bitaxeorg/bitaxeproto/3d/DISST7789-176x320.STEP

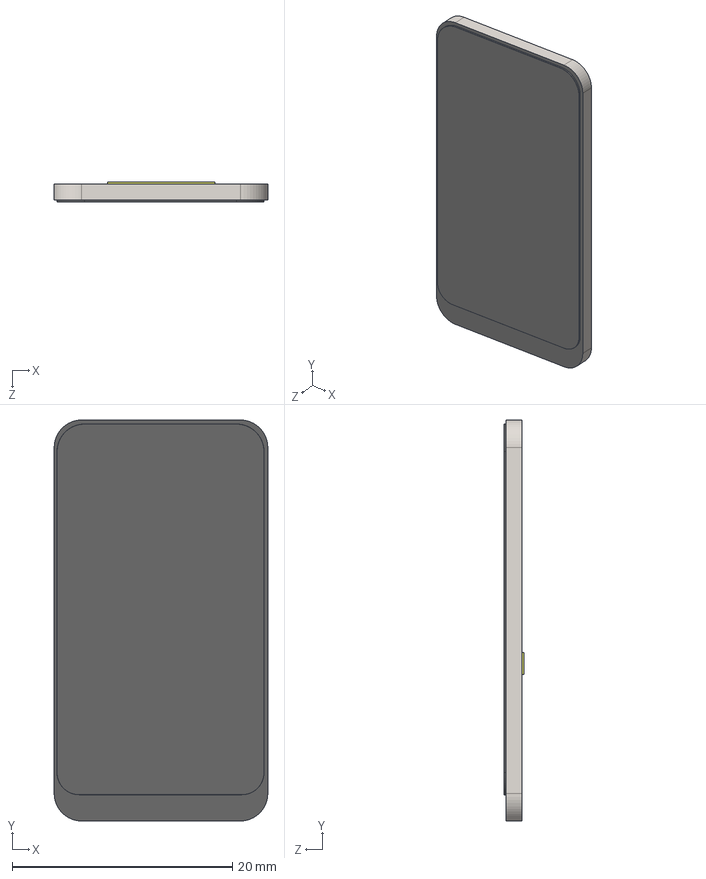
[picture p16: CAD file, 2026-05-12]
3d/DISST7789-176x320.STEP
19.4 x 36.4 x 1.86 mm
