bitaxeorg/bitaxeproto/3d/TXB0104RGYR.STEP

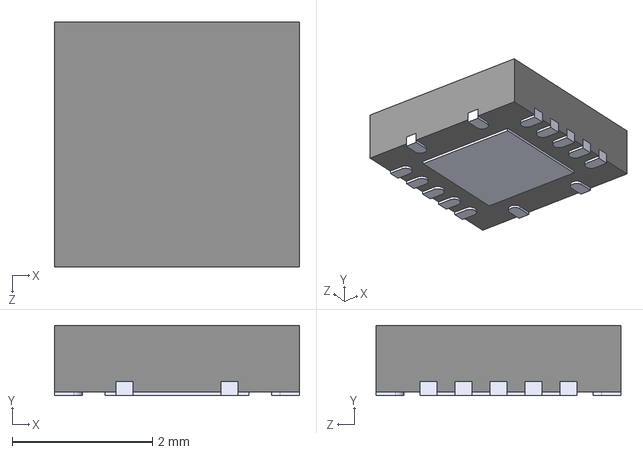
[picture p17: CAD file, 2026-05-12]
3d/TXB0104RGYR.STEP
3.50 x 1.00 x 3.50 mm
