bitaxeorg/bitaxeproto/3d/ESP32-S3-WROOM-1-N8R2--3DModel-STEP-56544.STEP

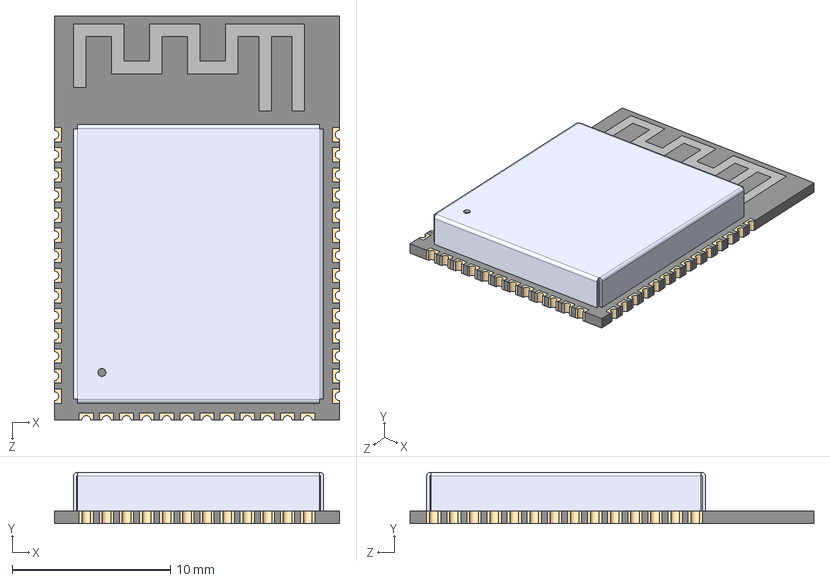
[picture p18: CAD file, 2026-05-12]
3d/ESP32-S3-WROOM-1-N8R2--3DModel-STEP-56544.STEP
18.0 x 3.25 x 25.5 mm
