bitaxeorg/bitaxeproto/3d/TPS546D24ARVFR.step

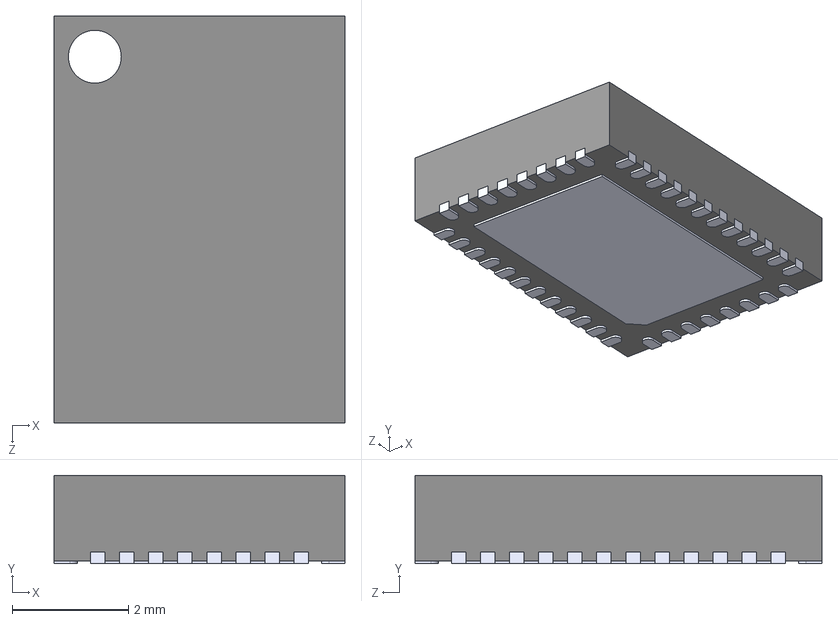
[picture p19: CAD file, 2026-05-12]
3d/TPS546D24ARVFR.step
5.00 x 1.52 x 7.00 mm
