bitaxeorg/bitaxeproto/3d/BitaxeGT_heatsink.step

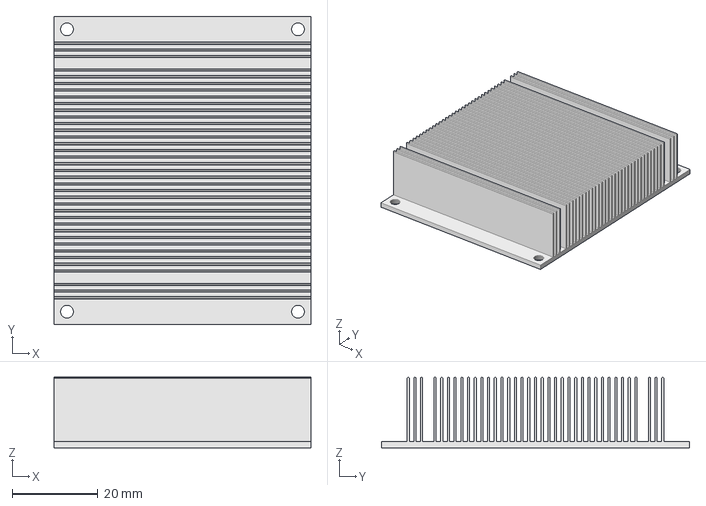
[picture p20: CAD file, 2026-05-12]
3d/BitaxeGT_heatsink.step
60.0 x 72.0 x 16.5 mm
