bitaxeorg/bitaxeproto/3d/BM04B-SRSS-TB.STEP

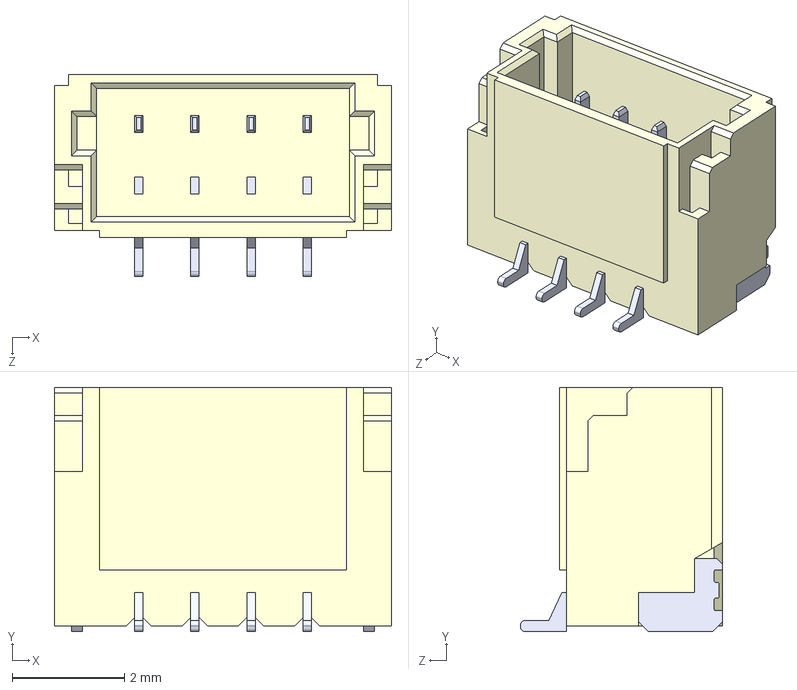
[picture p21: CAD file, 2026-05-12]
3d/BM04B-SRSS-TB.STEP
6.00 x 4.35 x 3.60 mm
