bitaxeorg/bitaxeproto/3d/ECS-3225MV-500-CN-TR.STEP

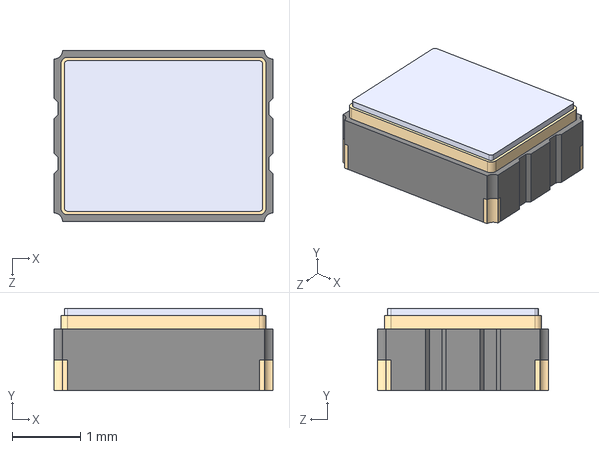
[picture p22: CAD file, 2026-05-12]
3d/ECS-3225MV-500-CN-TR.STEP
3.20 x 1.20 x 2.50 mm
