bitaxeorg/bitaxeproto/3d/BM1368xx.stp

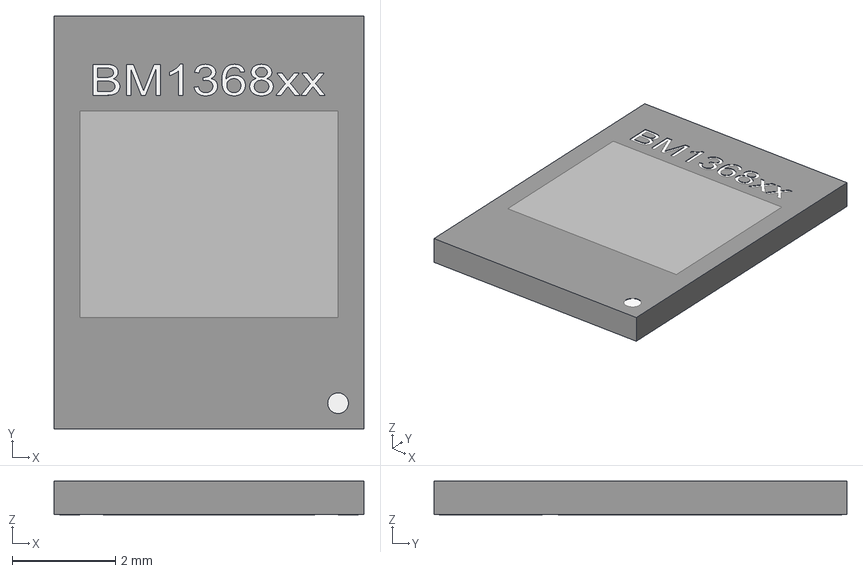
[picture p23: CAD file, 2026-05-12]
3d/BM1368xx.stp
6.00 x 8.00 x 0.65 mm
