bitaxeorg/bitaxeproto/3d/CUI_DEVICES_PJ-036AH-SMT-TR.step

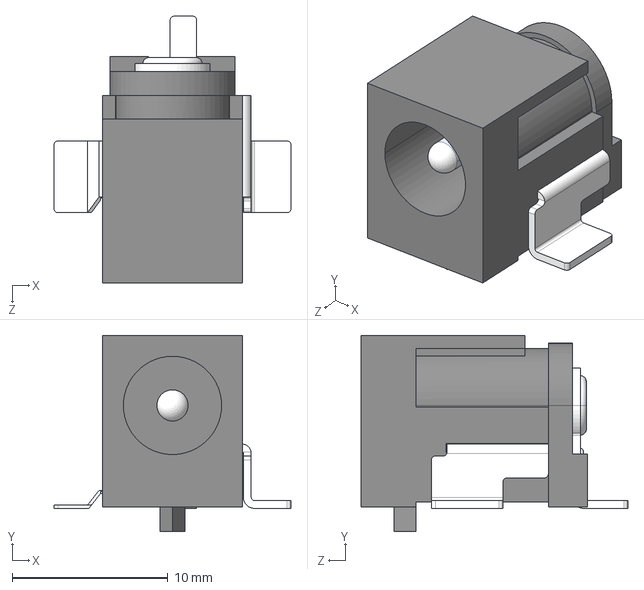
[picture p24: CAD file, 2026-05-12]
3d/CUI_DEVICES_PJ-036AH-SMT-TR.step
15.2 x 12.6 x 17.1 mm
