bitaxeorg/bitaxeproto/3d/SLC1175-271MEC_COC.step

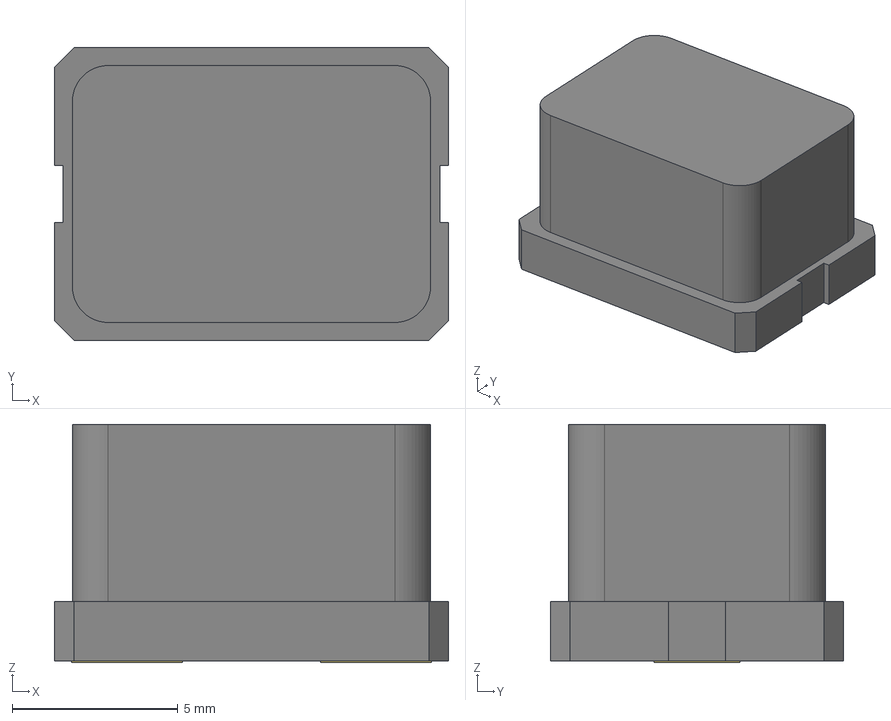
[picture p25: CAD file, 2026-05-12]
3d/SLC1175-271MEC_COC.step
11.9 x 8.83 x 7.19 mm
