bitaxeorg/bitaxeproto/3d/FPC-SMD_P0.50-8P_FGS-XJ-H2.0.step

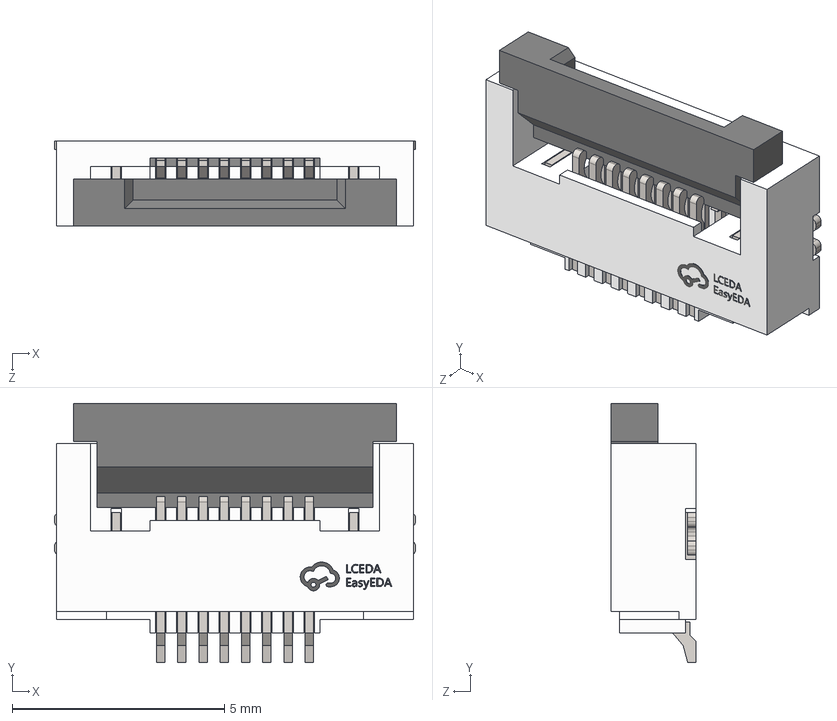
[picture p26: CAD file, 2026-05-12]
3d/FPC-SMD_P0.50-8P_FGS-XJ-H2.0.step
8.50 x 6.10 x 2.01 mm
