bitaxeorg/bitaxeproto/3d/USB_10118193-0001LF.STEP

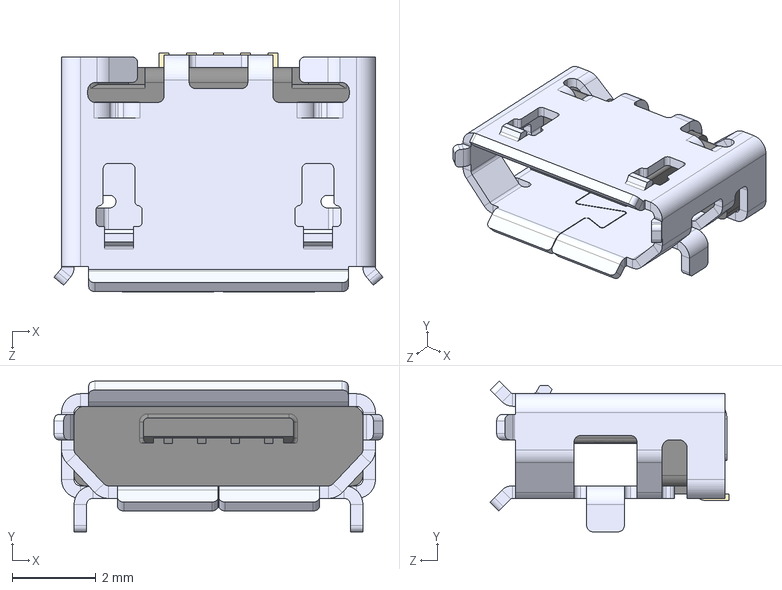
[picture p27: CAD file, 2026-05-12]
3d/USB_10118193-0001LF.STEP
7.86 x 3.60 x 5.71 mm
