bitaxeorg/bitaxeproto/3d/TPSM863257RDXR--3DModel-STEP-510211.STEP

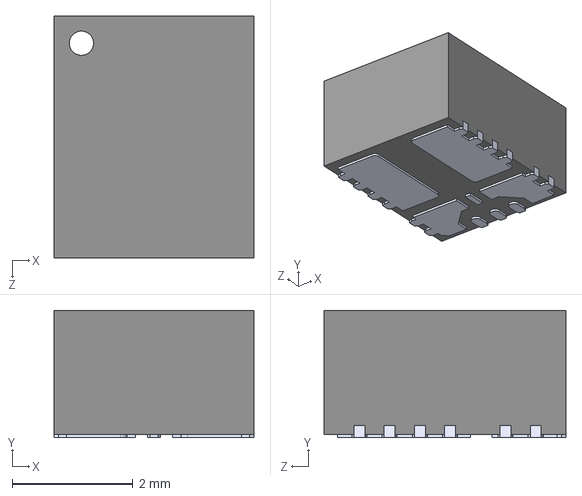
[picture p29: CAD file, 2026-05-12]
3d/TPSM863257RDXR--3DModel-STEP-510211.STEP
3.30 x 2.10 x 4.00 mm
