bitaxeorg/bitaxeproto/3d/TSOT-23-5_RIT.step

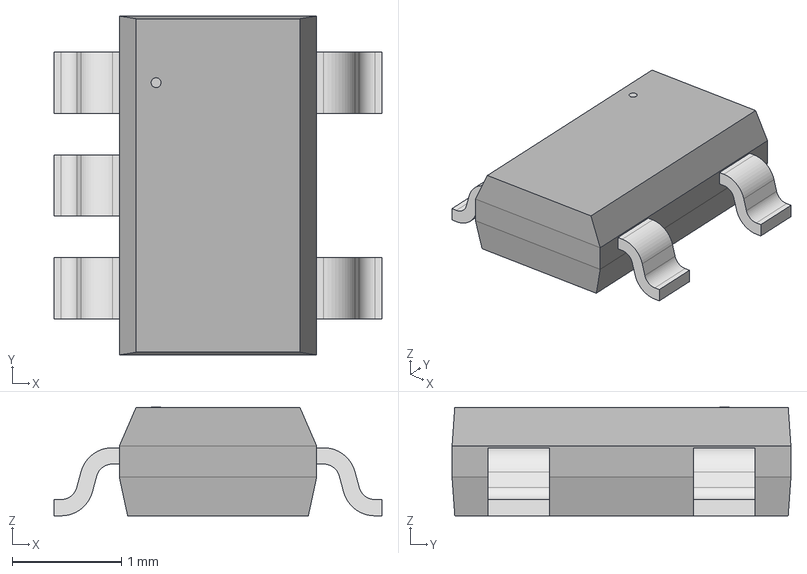
[picture p30: CAD file, 2026-05-12]
3d/TSOT-23-5_RIT.step
3.00 x 3.10 x 0.993 mm
