bitaxeorg/bitaxeproto/3d/RGY0016A.stp

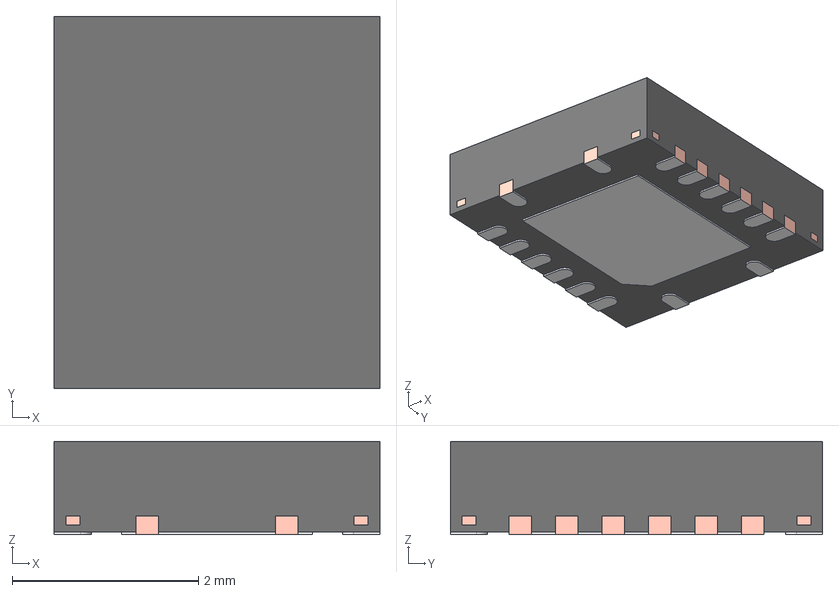
[picture p31: CAD file, 2026-05-12]
3d/RGY0016A.stp
3.50 x 4.00 x 1.00 mm
FRAME
PIN1_AREA
