bitaxeorg/bitaxeproto/3d/FFC2B35-08-T.STEP

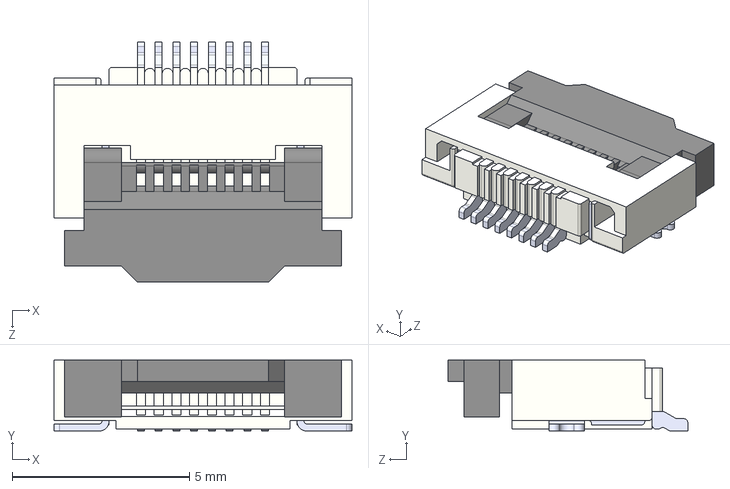
[picture p32: CAD file, 2026-05-12]
3d/FFC2B35-08-T.STEP
8.40 x 2.00 x 6.76 mm
