bitaxeorg/bitaxeproto/3d/XTAL_SC32S-7PF20PPM_EPS.step

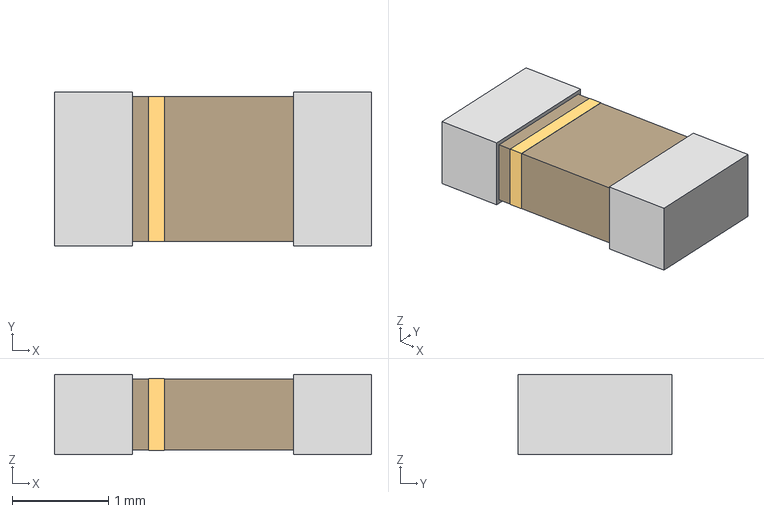
[picture p34: CAD file, 2026-05-12]
3d/XTAL_SC32S-7PF20PPM_EPS.step
3.30 x 1.60 x 0.838 mm
