bitaxeorg/bitaxeproto/3d/BQB0016A.stp

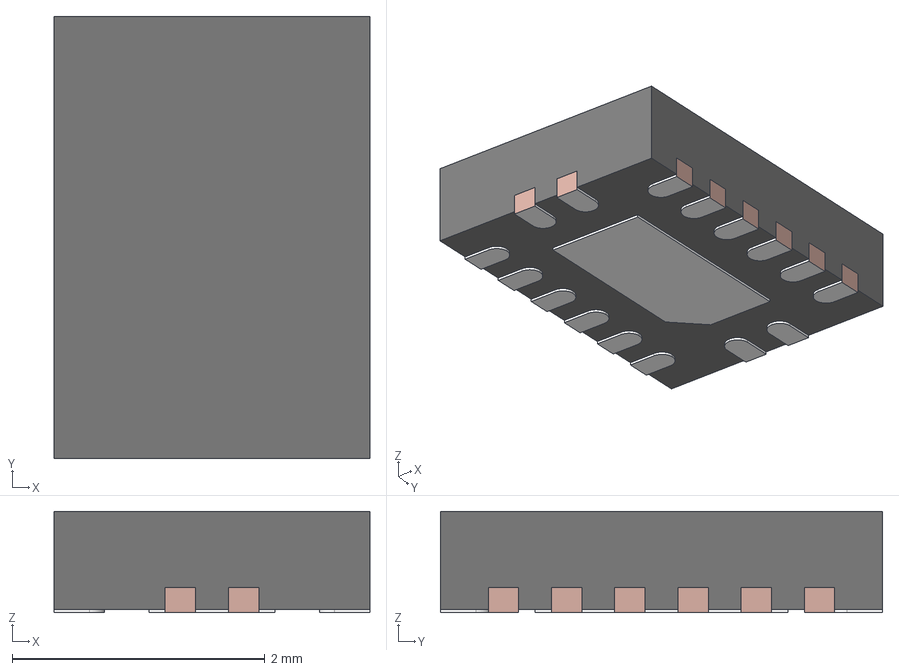
[picture p35: CAD file, 2026-05-12]
3d/BQB0016A.stp
2.50 x 3.50 x 0.8 mm
FRAME
