bitaxeorg/bitaxeproto/3d/RP-006426-DD-A-Raspberry Pi Pico 2 3D CAD Model R5 24 07 24.step

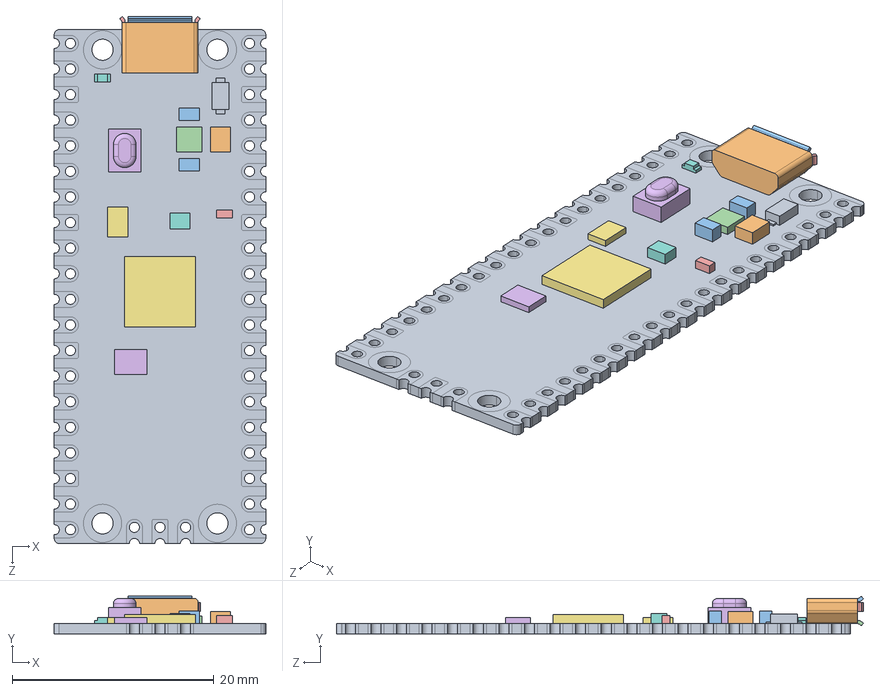
[picture p37: CAD file, 2026-05-12]
3d/RP-006426-DD-A-Raspberry Pi Pico 2 3D CAD Model R5 24 07 24.step
21.0 x 3.73 x 52.3 mm
PICO_REF_BOARD
PICO_REF_USB
PICO_REF_SWITCH
PICO_REF_MICROCONTROLLER
PICO_REF_LED
PICO_REF_COMP_1
PICO_REF_COMP_2
PICO_REF_COMP_3 x 2
PICO_REF_COMP_4
PICO_REF_COMP_5
PICO_REF_COMP_6
PICO_REF_COMP_7
PICO_REF_INDUCTOR
