bitaxeorg/bitaxeproto/3d/SOT-23-5_M5_MCH.step

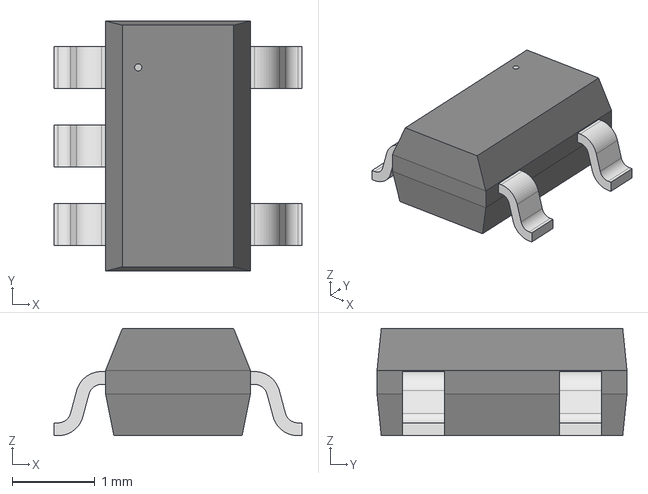
[picture p38: CAD file, 2026-05-12]
3d/SOT-23-5_M5_MCH.step
3.00 x 3.02 x 1.30 mm
