bitaxeorg/bitaxeproto/3d/RaspberryPi_Pico_W_AddedHeaders.step

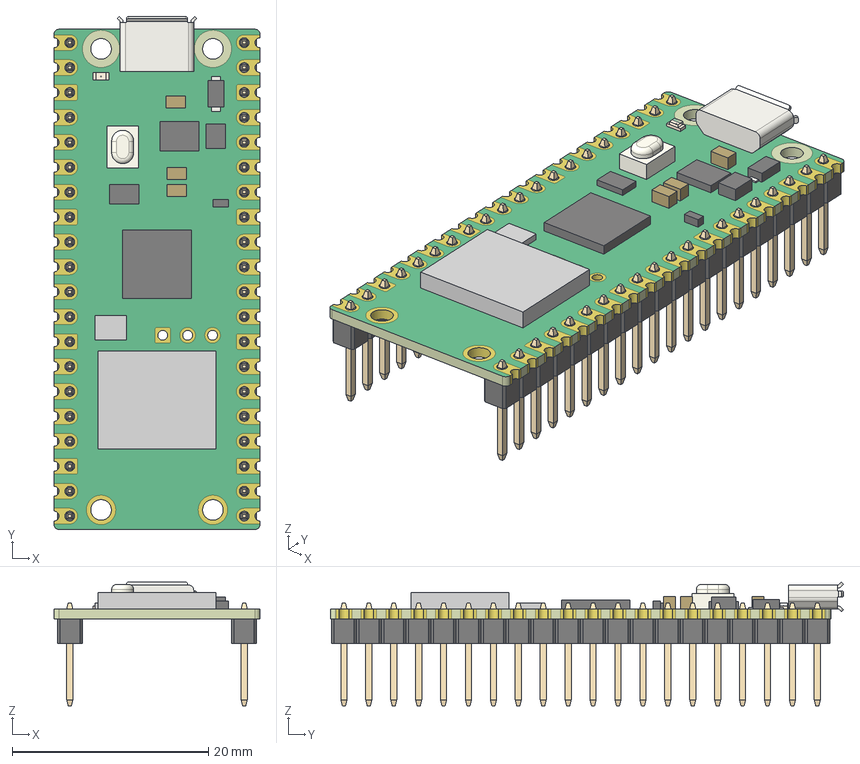
[picture p39: CAD file, 2026-05-12]
3d/RaspberryPi_Pico_W_AddedHeaders.step
21.0 x 52.3 x 12.6 mm
