bitaxeorg/bitaxeproto/3d/GT heatsink.step

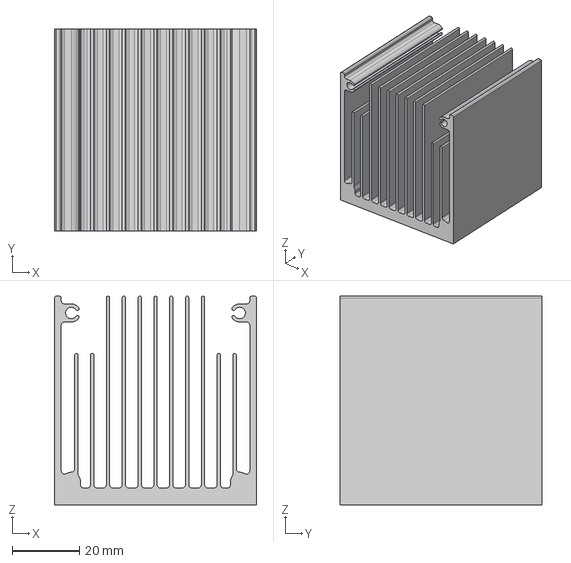
[picture p40: CAD file, 2026-05-12]
3d/GT heatsink.step
60.0 x 60.0 x 62.0 mm
