bitaxeorg/bitaxeproto/3d/DQH0008A.stp

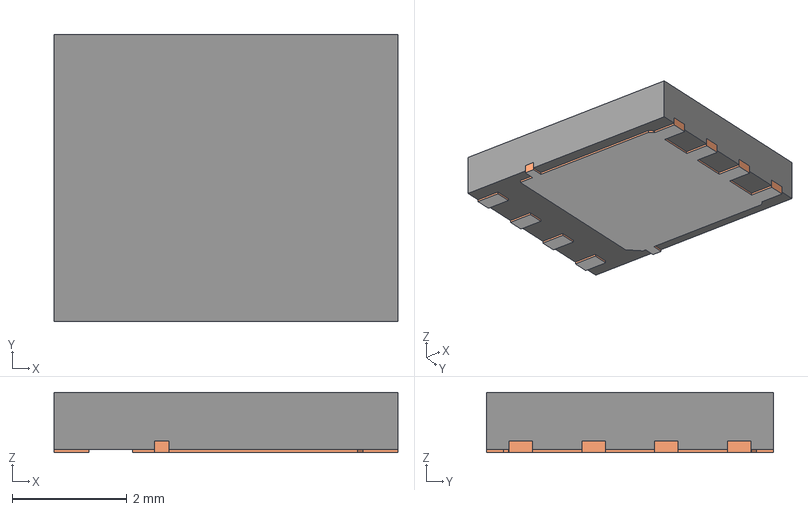
[picture p41: CAD file, 2026-05-12]
3d/DQH0008A.stp
6.00 x 5.00 x 1.05 mm
BODY-SON
FRAME-DQH0008A
PIN1-ID
