bitaxeorg/bitaxeproto/3d/DHVQFN14_SOT762-1_NEX.step

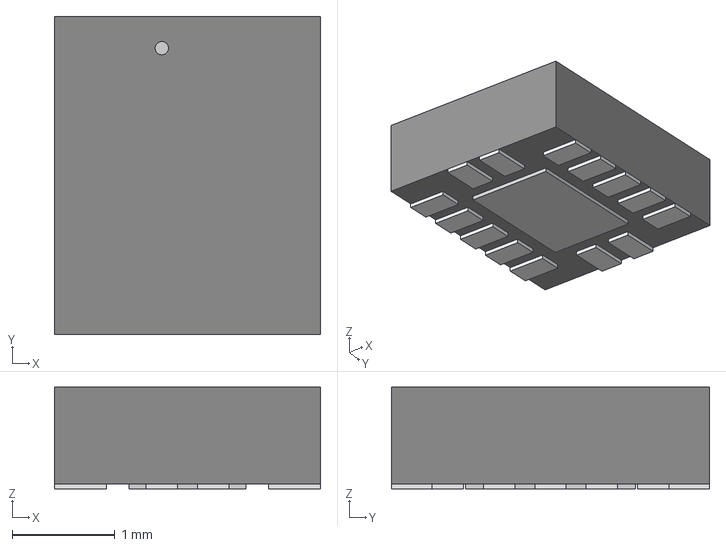
[picture p42: CAD file, 2026-05-12]
3d/DHVQFN14_SOT762-1_NEX.step
2.59 x 3.10 x 0.993 mm
