bitaxeorg/bitaxeproto/3d/Bitaxe_Heatsink.step

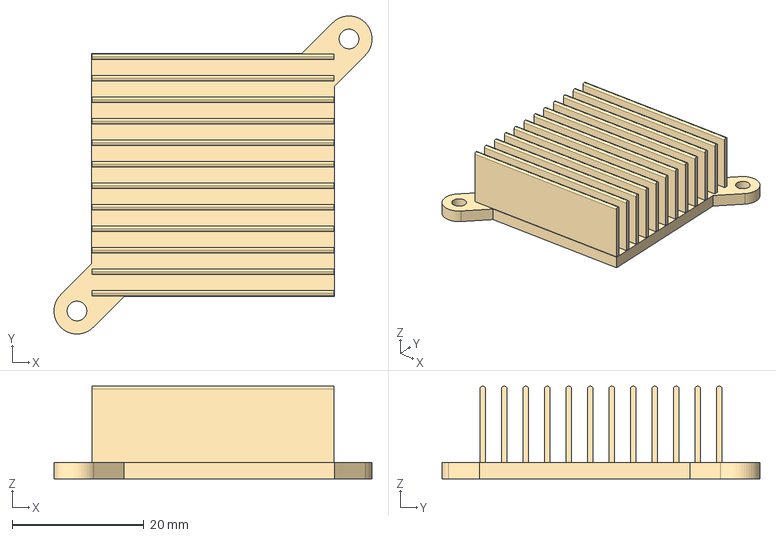
[picture p43: CAD file, 2026-05-12]
3d/Bitaxe_Heatsink.step
48.4 x 48.4 x 14.1 mm
