bitaxeorg/bitaxeproto/3d/oscillator3.2x2.5.step

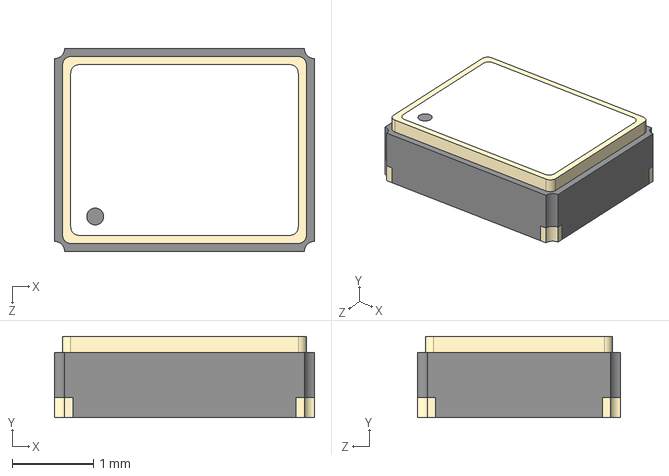
[picture p44: CAD file, 2026-05-12]
3d/oscillator3.2x2.5.step
3.20 x 1.00 x 2.50 mm
