bitaxeorg/bitaxeproto/3d/TPSM82903SISR.stp

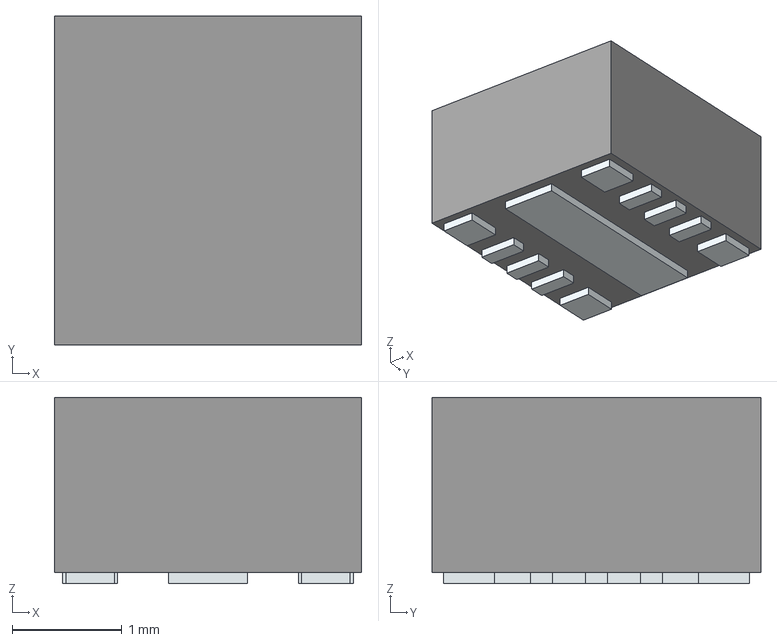
[picture p45: CAD file, 2026-05-12]
3d/TPSM82903SISR.stp
2.80 x 3.00 x 1.70 mm
Pins
