bitaxeorg/bitaxeproto/3d/c-63862-1-r-3d.stp

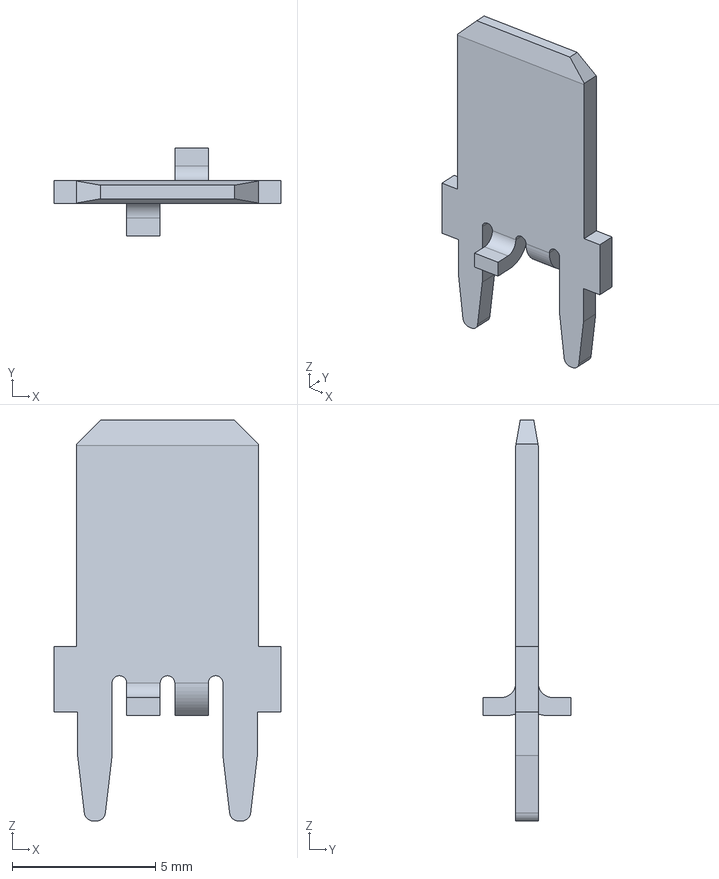
[picture p46: CAD file, 2026-05-12]
3d/c-63862-1-r-3d.stp
7.92 x 3.07 x 14.0 mm
