bitaxeorg/bitaxeproto/3d/2R5TPE220MAFB.step

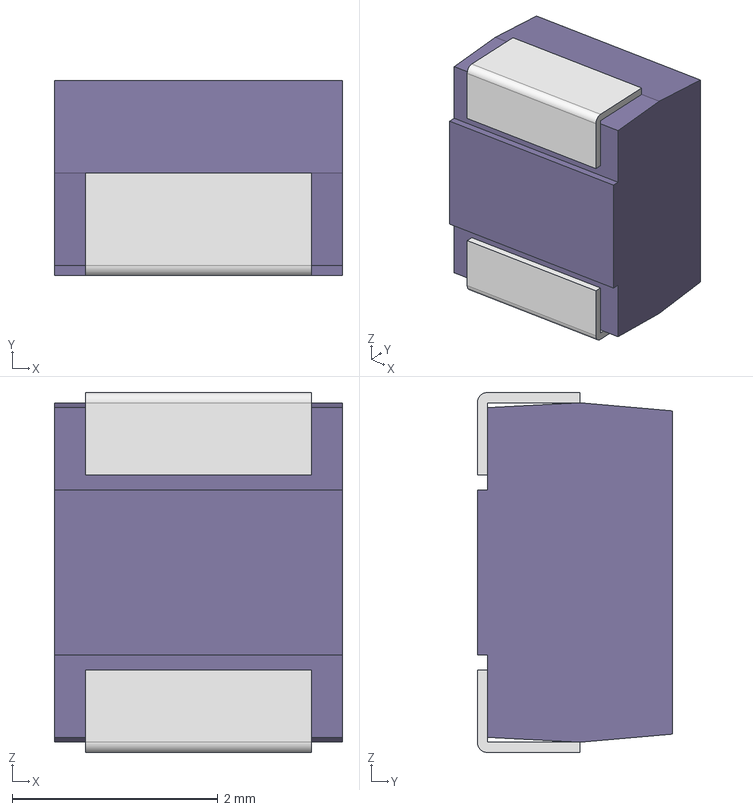
[picture p47: CAD file, 2026-05-12]
3d/2R5TPE220MAFB.step
2.80 x 1.90 x 3.50 mm
mold-B2
flame-B2 x 2
