bitaxeorg/bitaxeproto/3d/USON-8_UX_2x3x0p6_WIN.step

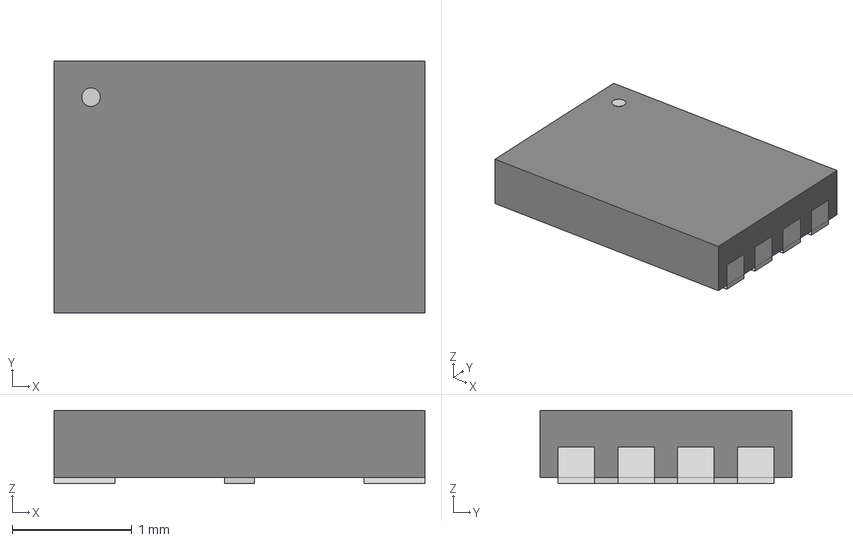
[picture p48: CAD file, 2026-05-12]
3d/USON-8_UX_2x3x0p6_WIN.step
3.10 x 2.11 x 0.612 mm
