bitaxeorg/bitaxeproto/3d/CS1213AG-tr.stp

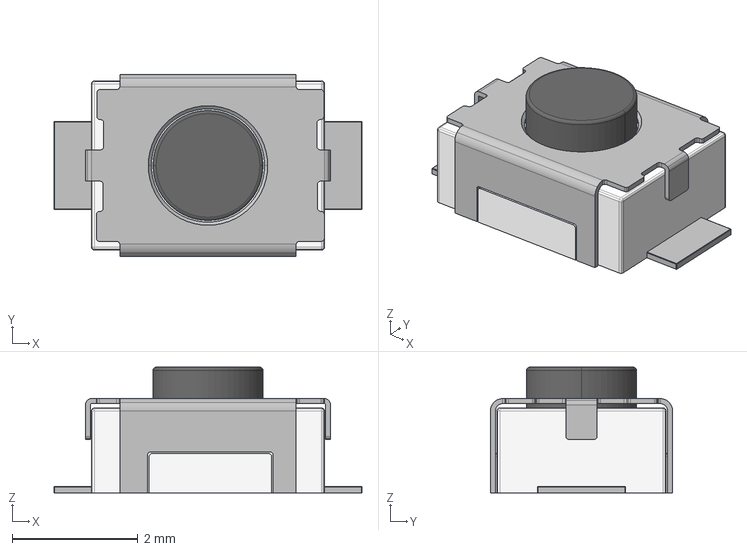
[picture p49: CAD file, 2026-05-12]
3d/CS1213AG-tr.stp
4.90 x 2.90 x 2.00 mm
