bitaxeorg/bitaxeproto/3d/Crystal_3225.step

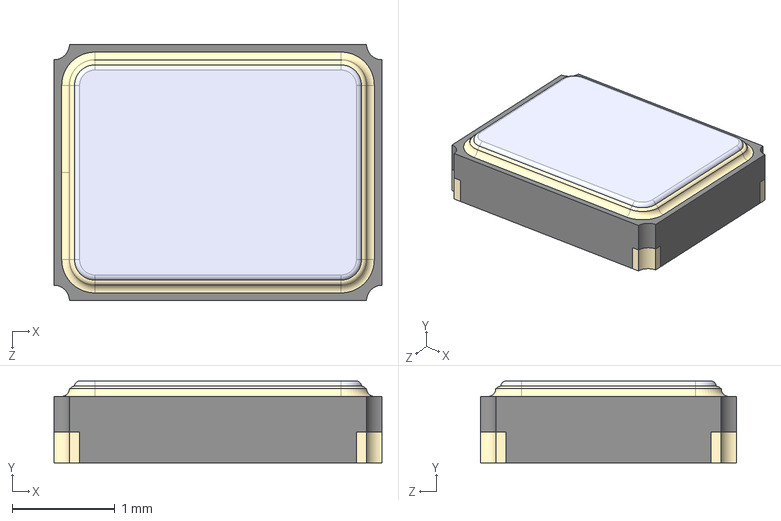
[picture p51: CAD file, 2026-05-12]
3d/Crystal_3225.step
3.20 x 0.8 x 2.50 mm
