bitaxeorg/bitaxeproto/3d/SN74AXC1T45DBVR.STEP

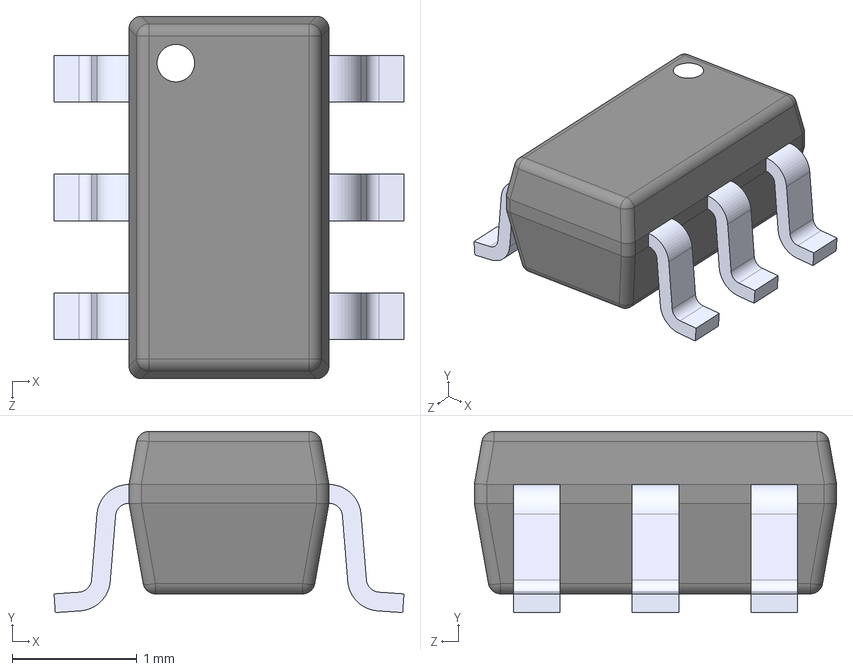
[picture p53: CAD file, 2026-05-12]
3d/SN74AXC1T45DBVR.STEP
2.80 x 1.45 x 2.90 mm
