bitaxeorg/bitaxeproto/3d/141_TL3330AFxxxQG.stp

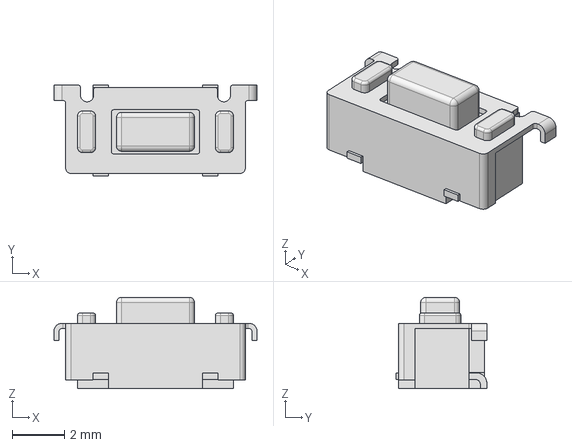
[picture p55: CAD file, 2026-05-12]
3d/141_TL3330AFxxxQG.stp
7.80 x 3.50 x 3.51 mm
