bitaxeorg/bitaxeproto/3d/c-1-1735042-0-m-3d.stp

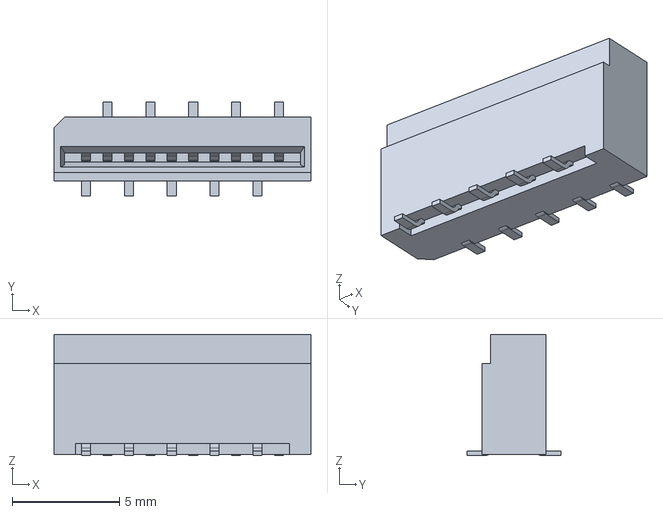
[picture p57: CAD file, 2026-05-12]
3d/c-1-1735042-0-m-3d.stp
12.0 x 4.40 x 5.65 mm
