bitaxeorg/bitaxeproto/3d/21-0164B_L622-1_MXM.step

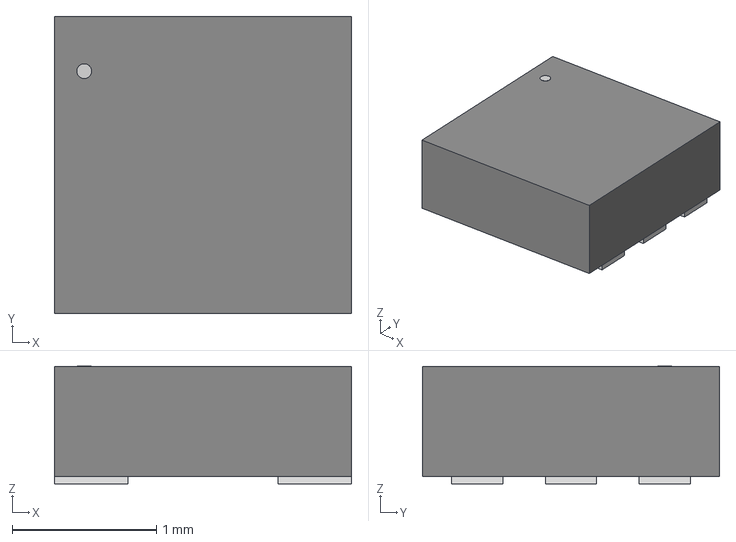
[picture p58: CAD file, 2026-05-12]
3d/21-0164B_L622-1_MXM.step
2.06 x 2.06 x 0.815 mm
