bitaxeorg/bitaxeproto/3d/SOD-323FL_UMD2__ROM.step

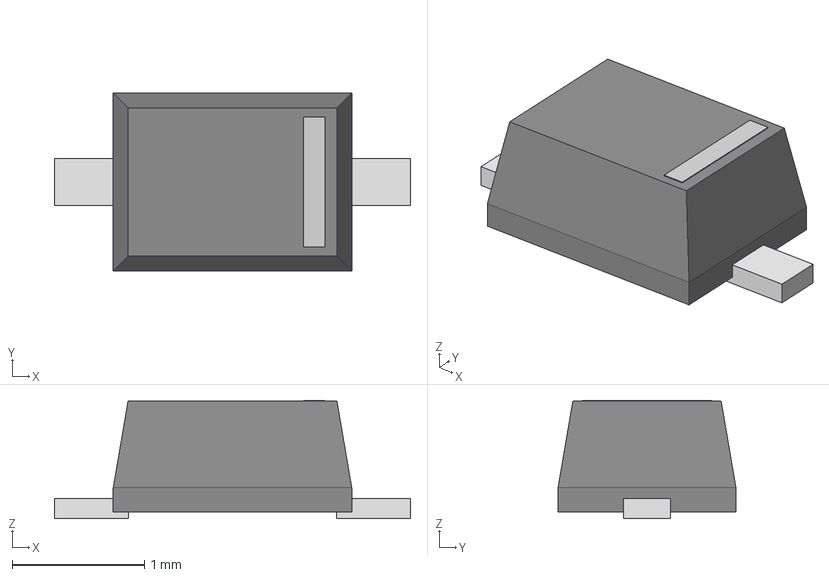
[picture p60: CAD file, 2026-05-12]
3d/SOD-323FL_UMD2__ROM.step
2.69 x 1.35 x 0.895 mm
