bitaxeorg/bitaxeproto/3d/CUI_DEVICES_PJ-002AH.step

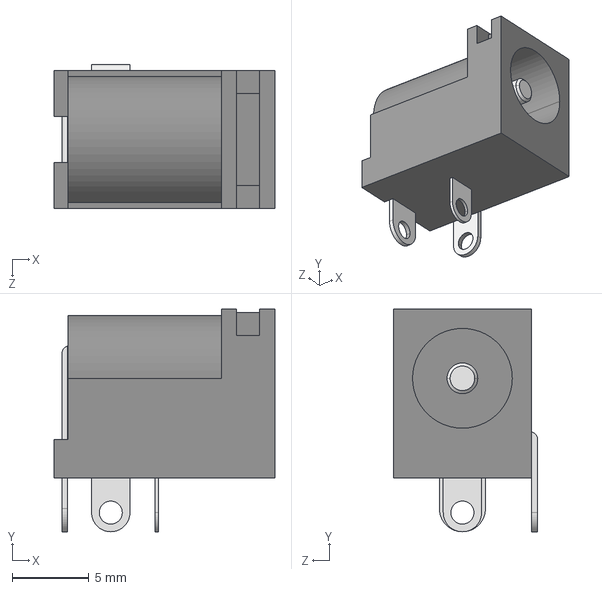
[picture p61: CAD file, 2026-05-12]
3d/CUI_DEVICES_PJ-002AH.step
14.4 x 14.5 x 9.40 mm
