bitaxeorg/bitaxeproto/3d/CUI_DEVICES_PJ-037AH.step

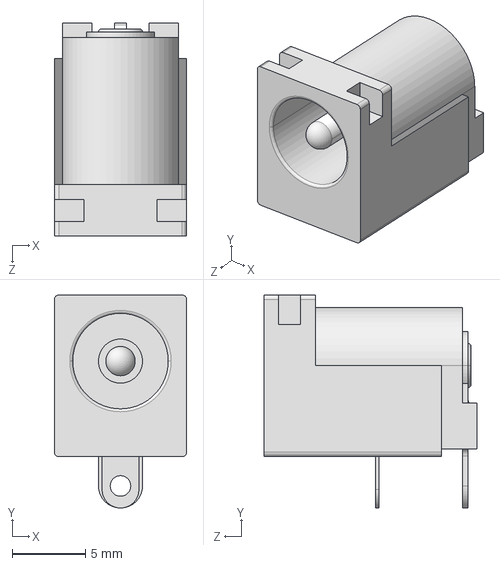
[picture p62: CAD file, 2026-05-12]
3d/CUI_DEVICES_PJ-037AH.step
9.00 x 14.5 x 14.5 mm
