bitaxeorg/bitaxeproto/3d/SMV_z90.stp

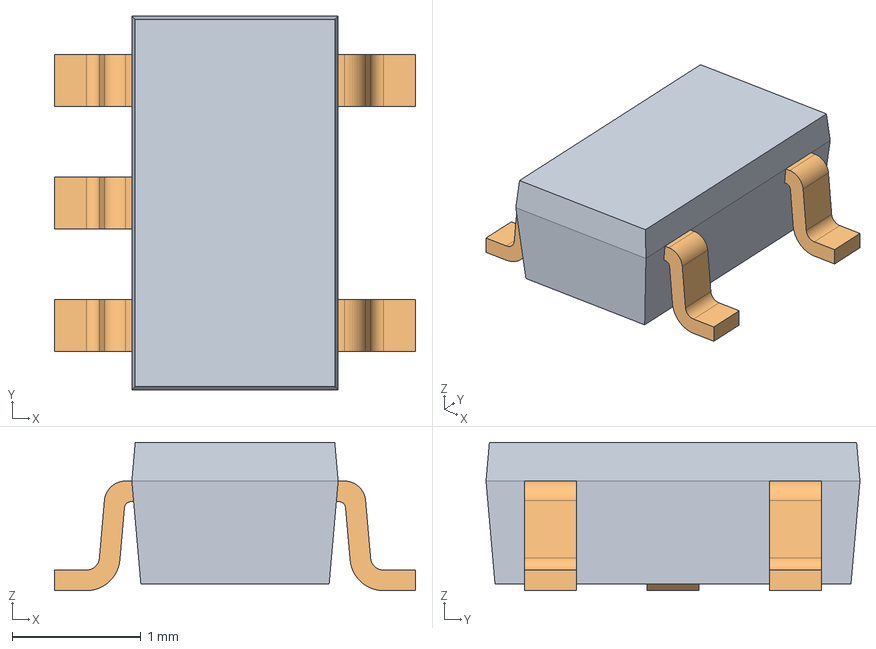
[picture p64: CAD file, 2026-05-12]
3d/SMV_z90.stp
2.80 x 2.90 x 1.15 mm
