bitaxeorg/bitaxeproto/3d/XRCGB27M120F3M10R0_MUR.step

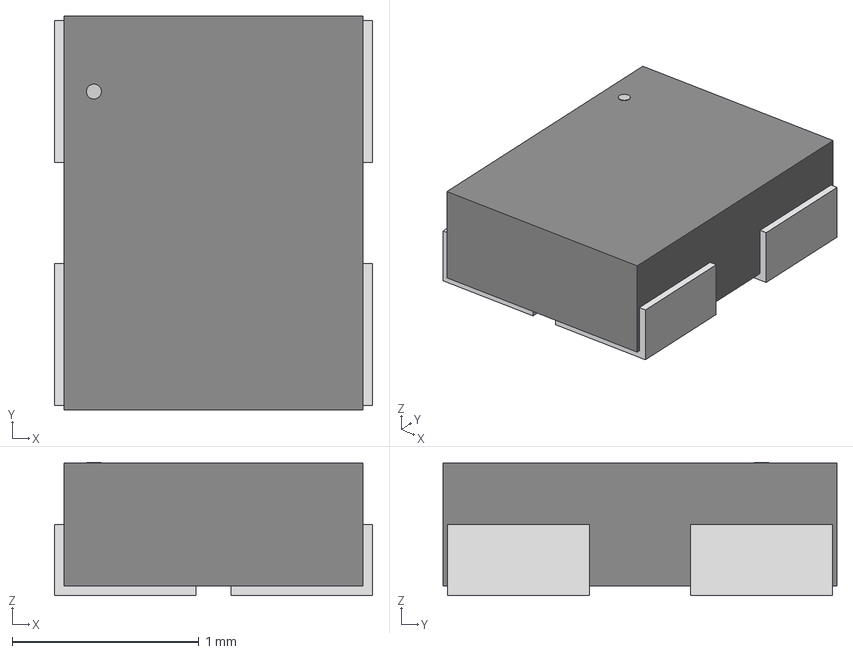
[picture p65: CAD file, 2026-05-12]
3d/XRCGB27M120F3M10R0_MUR.step
1.70 x 2.11 x 0.714 mm
