bitaxeorg/bitaxeproto/3d/DQN0004A.stp

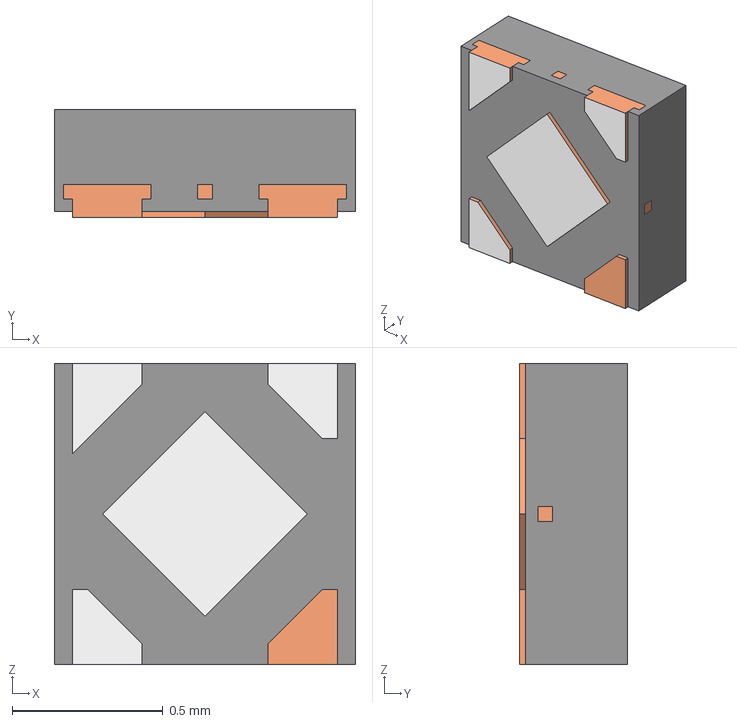
[picture p68: CAD file, 2026-05-12]
3d/DQN0004A.stp
1.00 x 0.36 x 1.00 mm
MOLD-SNB04A
FRAME-SNB04A
