bitaxeorg/bitaxeproto/3d/IND_-1R5MC_SUM.step

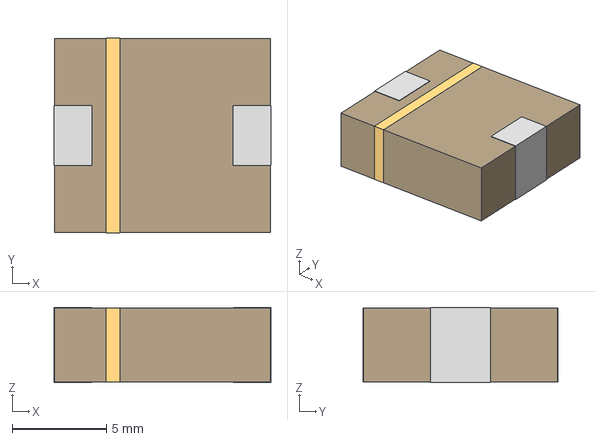
[picture p69: CAD file, 2026-05-12]
3d/IND_-1R5MC_SUM.step
11.5 x 10.3 x 3.99 mm
