bitaxeorg/bitaxeproto/3d/XT30PW-M.stp

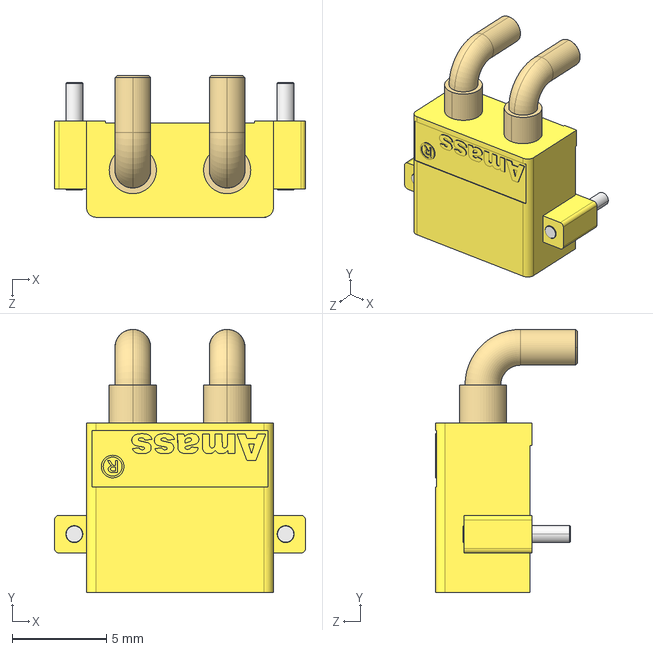
[picture p70: CAD file, 2026-05-12]
3d/XT30PW-M.stp
13.3 x 13.9 x 7.50 mm
