bitaxeorg/bitaxeproto/3d/Coilcraft-XAL1060.STEP

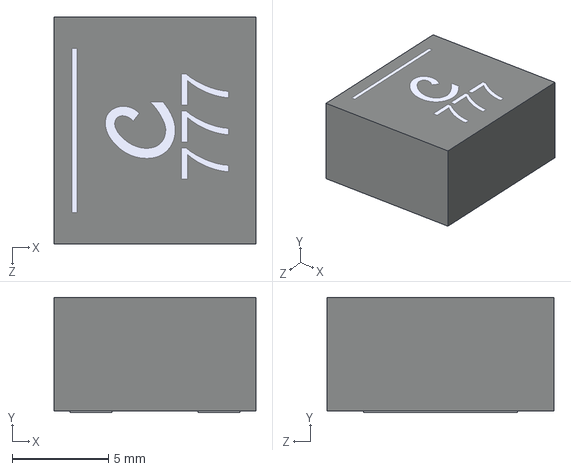
[picture p71: CAD file, 2026-05-12]
3d/Coilcraft-XAL1060.STEP
10.5 x 6.00 x 11.8 mm
