bitaxeorg/bitaxeproto/3d/bm1370.step

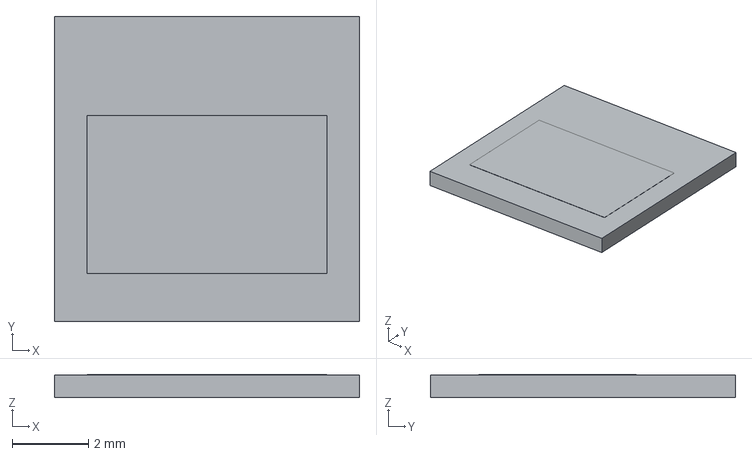
[picture p73: CAD file, 2026-05-12]
3d/bm1370.step
8.00 x 8.00 x 0.61 mm
