bitaxeorg/bitaxeproto/3d/DRL0006A.stp

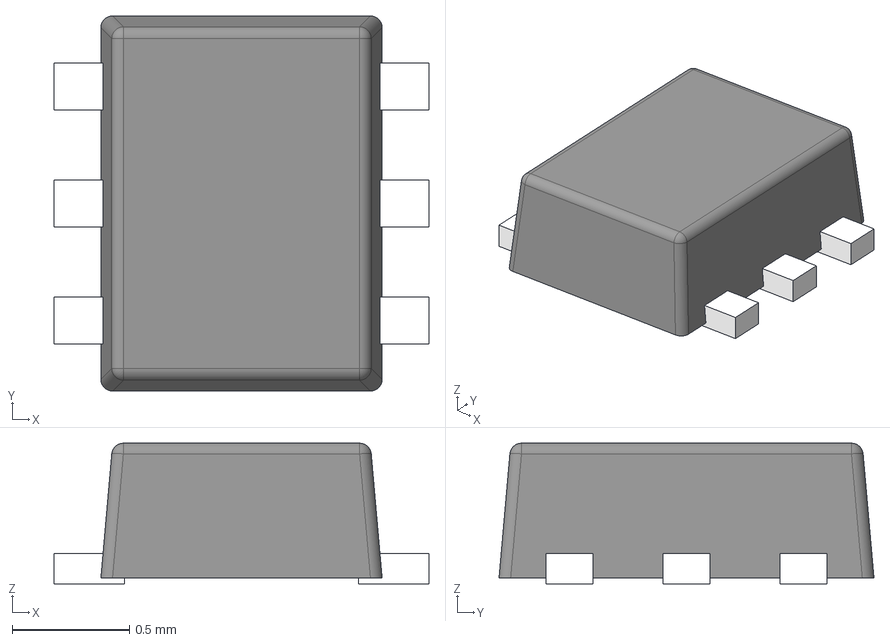
[picture p74: CAD file, 2026-05-12]
3d/DRL0006A.stp
1.60 x 1.60 x 0.6 mm
FRAME-DRL0006A
BODY-SOT
PIN1-ID
