bitaxeorg/bitaxeproto/3d/QFN16_4X4_MCH.step

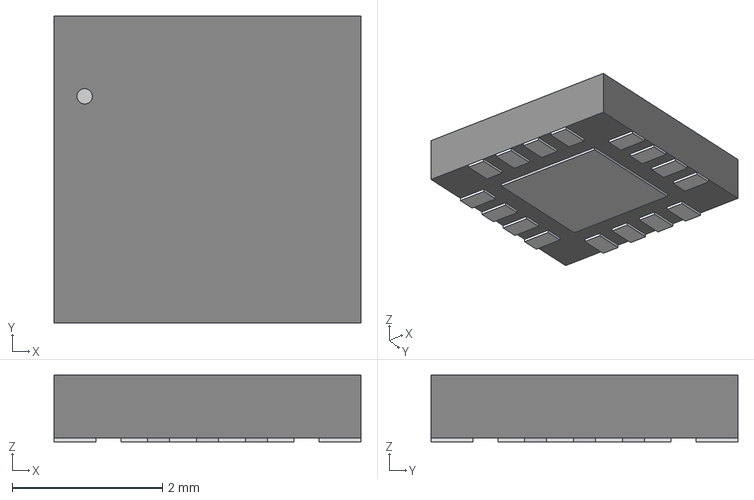
[picture p75: CAD file, 2026-05-12]
3d/QFN16_4X4_MCH.step
4.09 x 4.09 x 0.892 mm
