bitaxeorg/bitaxeproto/3d/DCK0006A.stp

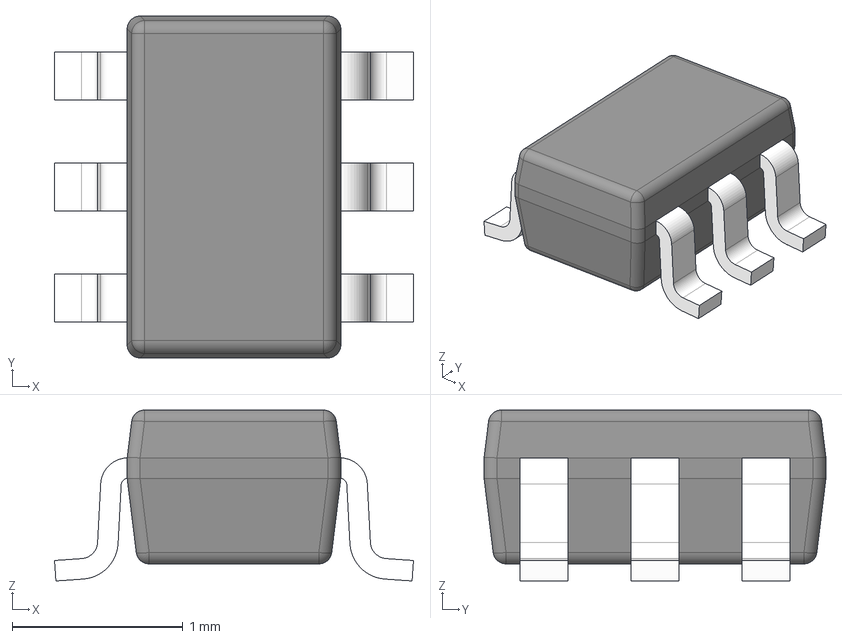
[picture p76: CAD file, 2026-05-12]
3d/DCK0006A.stp
2.10 x 2.00 x 1.00 mm
BODY-SOT
LEAD-SOT x 6
PIN1-ID
