bitaxeorg/bitaxeproto/3d/Fan 60x60x25mm.stp

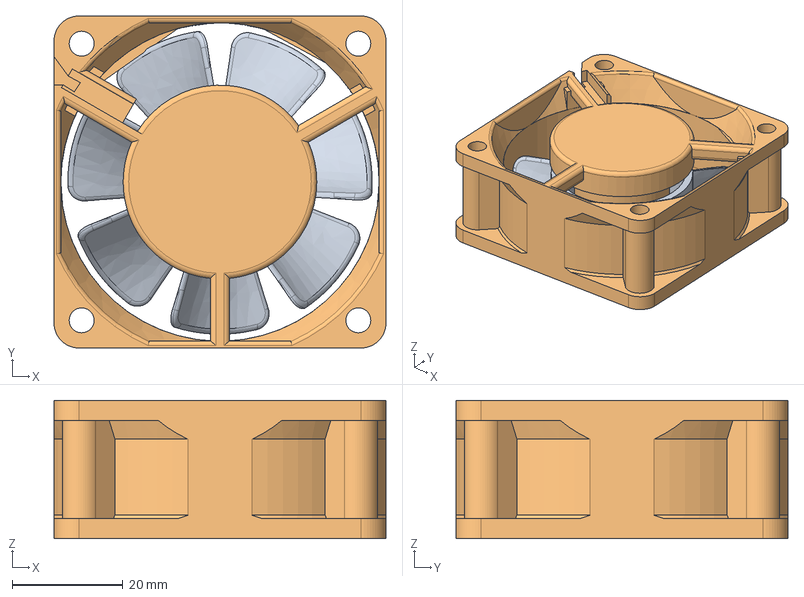
[picture p77: CAD file, 2026-05-12]
3d/Fan 60x60x25mm.stp
60.0 x 60.0 x 25.0 mm
