bitaxeorg/bitaxeproto/3d/BZM2model.step

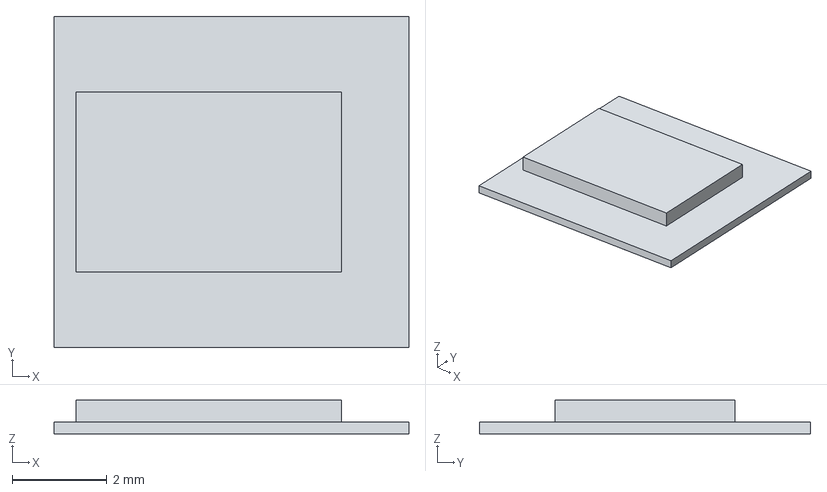
[picture p79: CAD file, 2026-05-12]
3d/BZM2model.step
7.50 x 7.00 x 0.71 mm
