bitaxeorg/bitaxeproto/3d/SW_CS1213AGF260_CRS.step

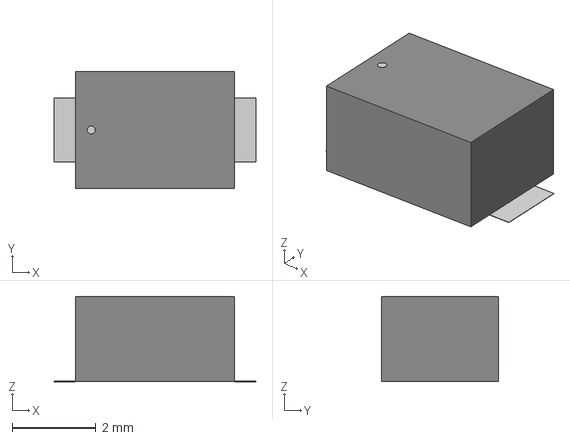
[picture p80: CAD file, 2026-05-12]
3d/SW_CS1213AGF260_CRS.step
4.83 x 2.79 x 2.04 mm
