bitaxeorg/bitaxeproto/3d/RaspberryPi_Pico_W.step

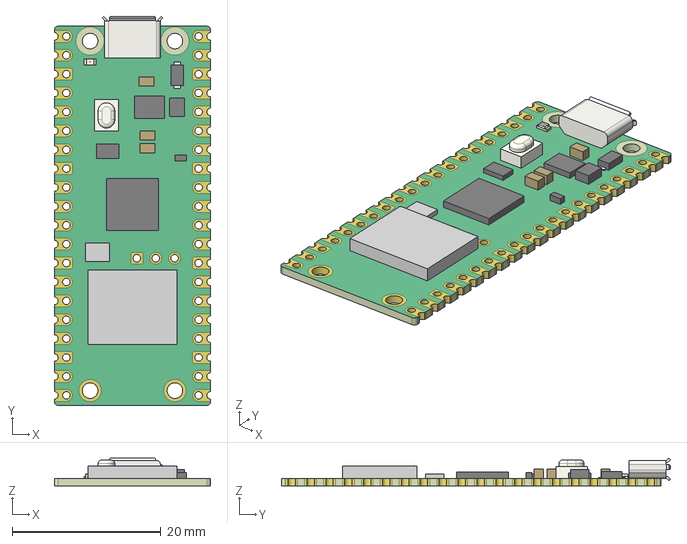
[picture p81: CAD file, 2026-05-12]
3d/RaspberryPi_Pico_W.step
21.0 x 52.3 x 3.75 mm
