bitaxeorg/bitaxeproto/3d/Coilcraft-SLC1175.STEP

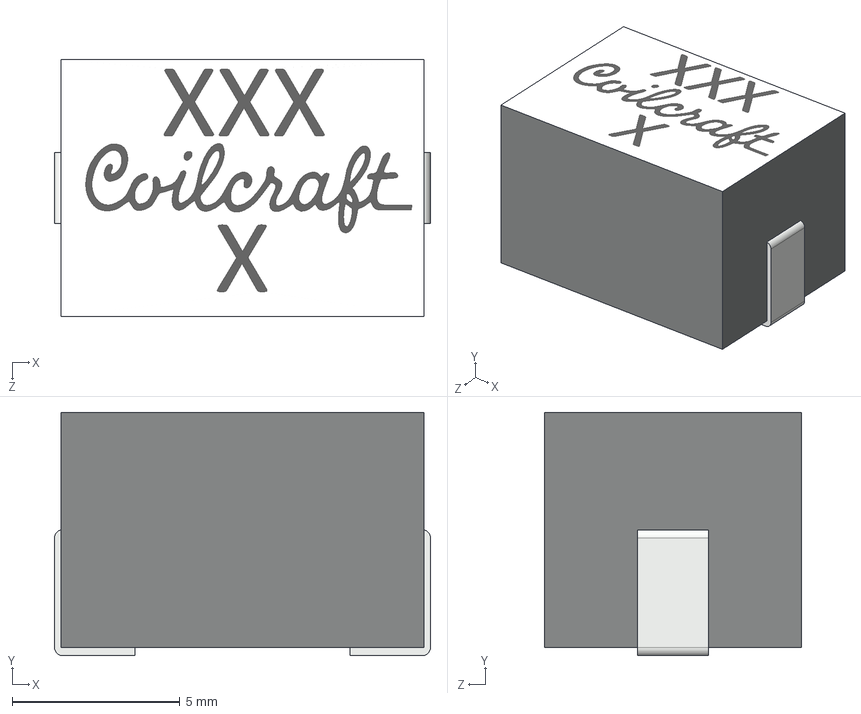
[picture p82: CAD file, 2026-05-12]
3d/Coilcraft-SLC1175.STEP
11.2 x 7.25 x 7.65 mm
